GEIGEIGEIST/TOTEM/docs/images/TOTEM_black_tenting_bottom.jpg

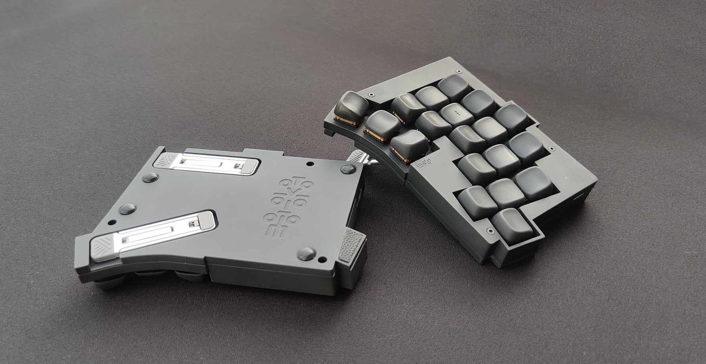
docs/images/TOTEM_black_tenting_bottom.jpg
