GEIGEIGEIST/TOTEM/docs/images/TOTEM_clayrender_01.jpg

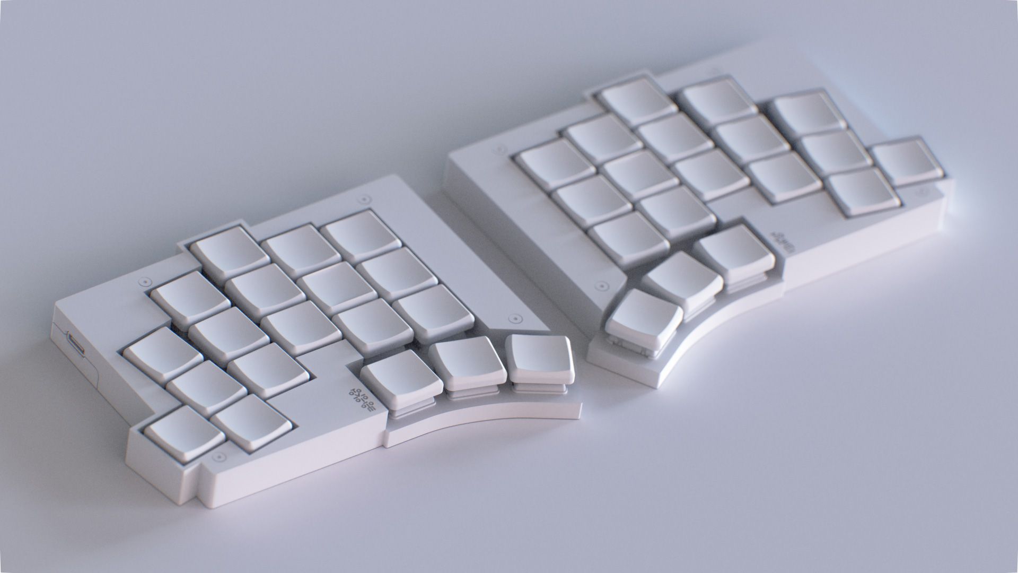
docs/images/TOTEM_clayrender_01.jpg
