GEIGEIGEIST/TOTEM/docs/images/TOTEM_clayrender_02.jpg

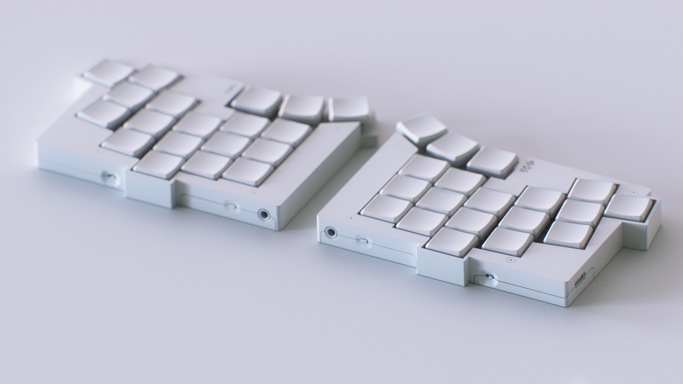
docs/images/TOTEM_clayrender_02.jpg
