GEIGEIGEIST/TOTEM/docs/images/TOTEM_layout.png

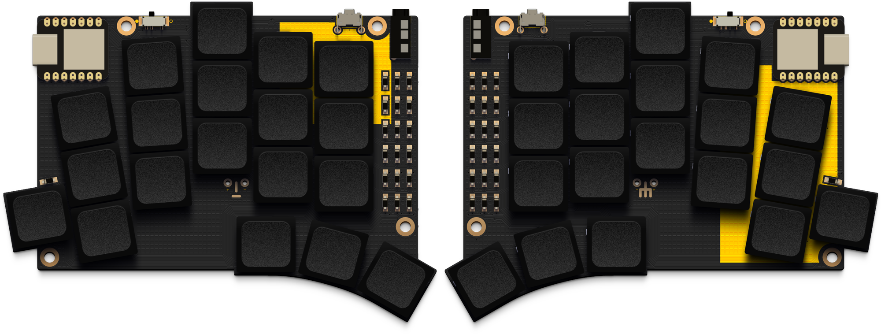
docs/images/TOTEM_layout.png
