GEIGEIGEIST/TOTEM/PCB/totem_0-3/TOTEM3D/PJ320A.STEP

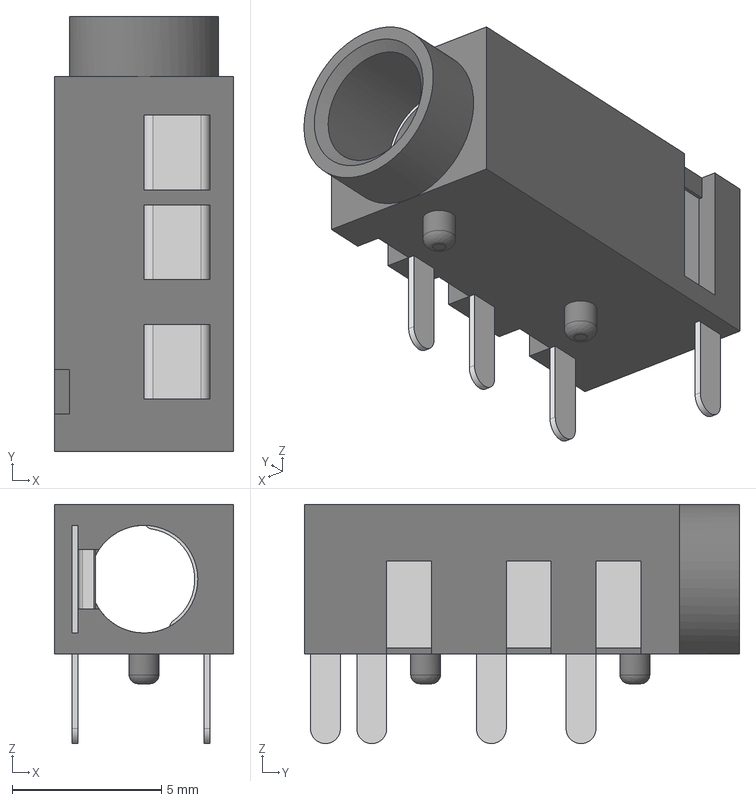
[picture p21: CAD file, 2022-11-10]
PCB/totem_0-3/TOTEM3D/PJ320A.STEP
6.00 x 14.6 x 8.00 mm
