GEIGEIGEIST/TOTEM/PCB/totem_0-3/TOTEM3D/D_SOD-123.step

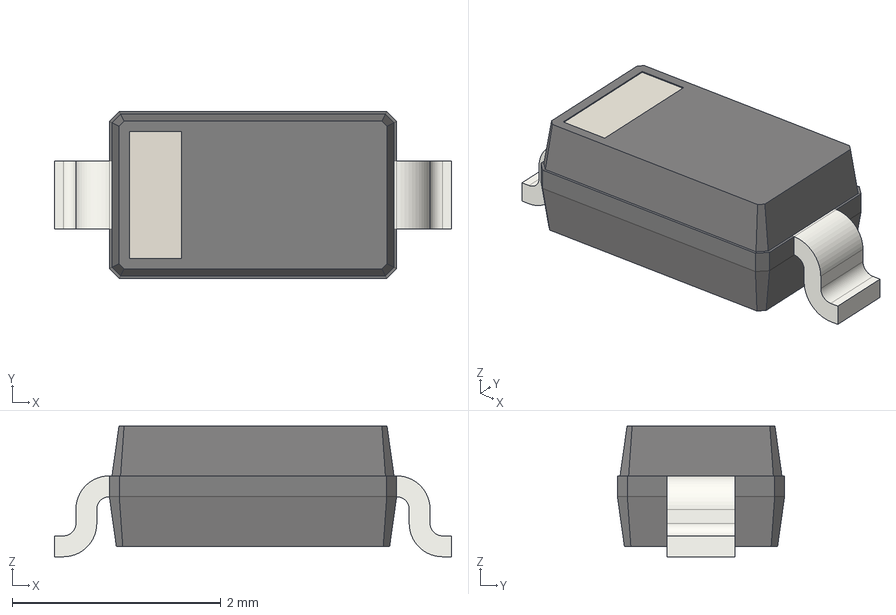
[picture p22: CAD file, 2022-11-10]
PCB/totem_0-3/TOTEM3D/D_SOD-123.step
3.80 x 1.60 x 1.25 mm
