GEIGEIGEIST/TOTEM/PCB/totem_0-3/TOTEM3D/xiao-ble-tht.step

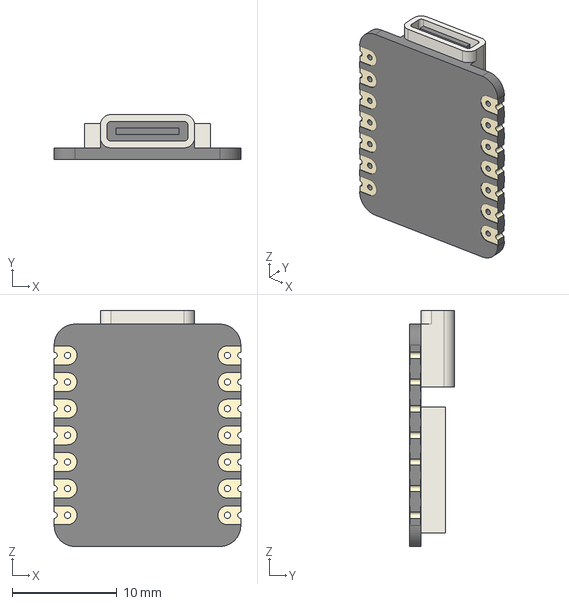
[picture p23: CAD file, 2022-11-10]
PCB/totem_0-3/TOTEM3D/xiao-ble-tht.step
17.8 x 4.27 x 22.5 mm
