GEIGEIGEIST/TOTEM/PCB/totem_0-3/TOTEM3D/MSK12C02.STEP

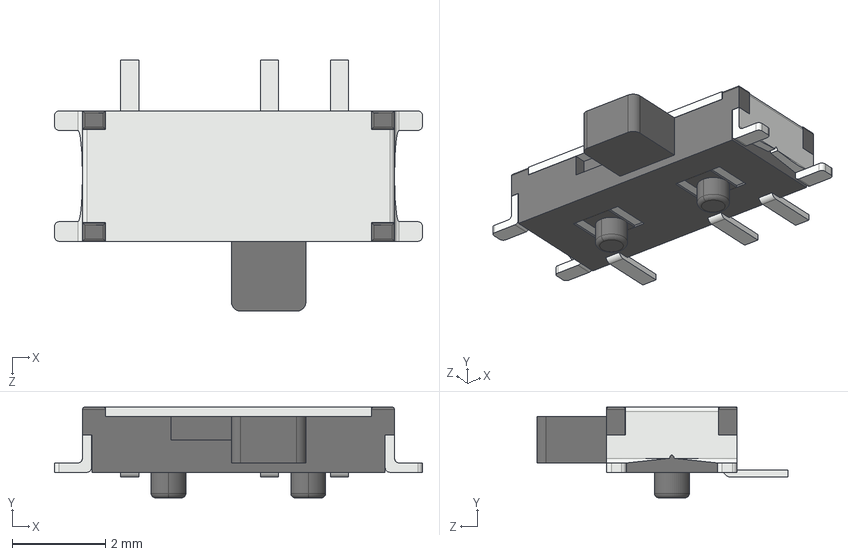
[picture p24: CAD file, 2022-11-10]
PCB/totem_0-3/TOTEM3D/MSK12C02.STEP
7.90 x 1.95 x 5.39 mm
