GEIGEIGEIST/TOTEM/PCB/totem_0-3/TOTEM3D/Kailh_socket_PG1350_optional.STEP

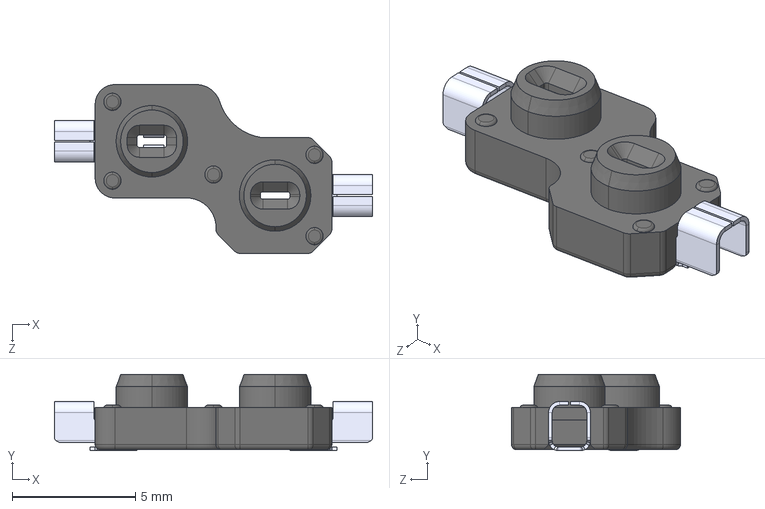
[picture p25: CAD file, 2022-11-10]
PCB/totem_0-3/TOTEM3D/Kailh_socket_PG1350_optional.STEP
12.9 x 3.09 x 6.85 mm
pin x 2
socket
