GEIGEIGEIST/TOTEM/PCB/totem_0-3/totem_0_3.kicad_sch

## KiCad design PCB/totem_0-3/totem_0_3.kicad_sch (2022-11-10)

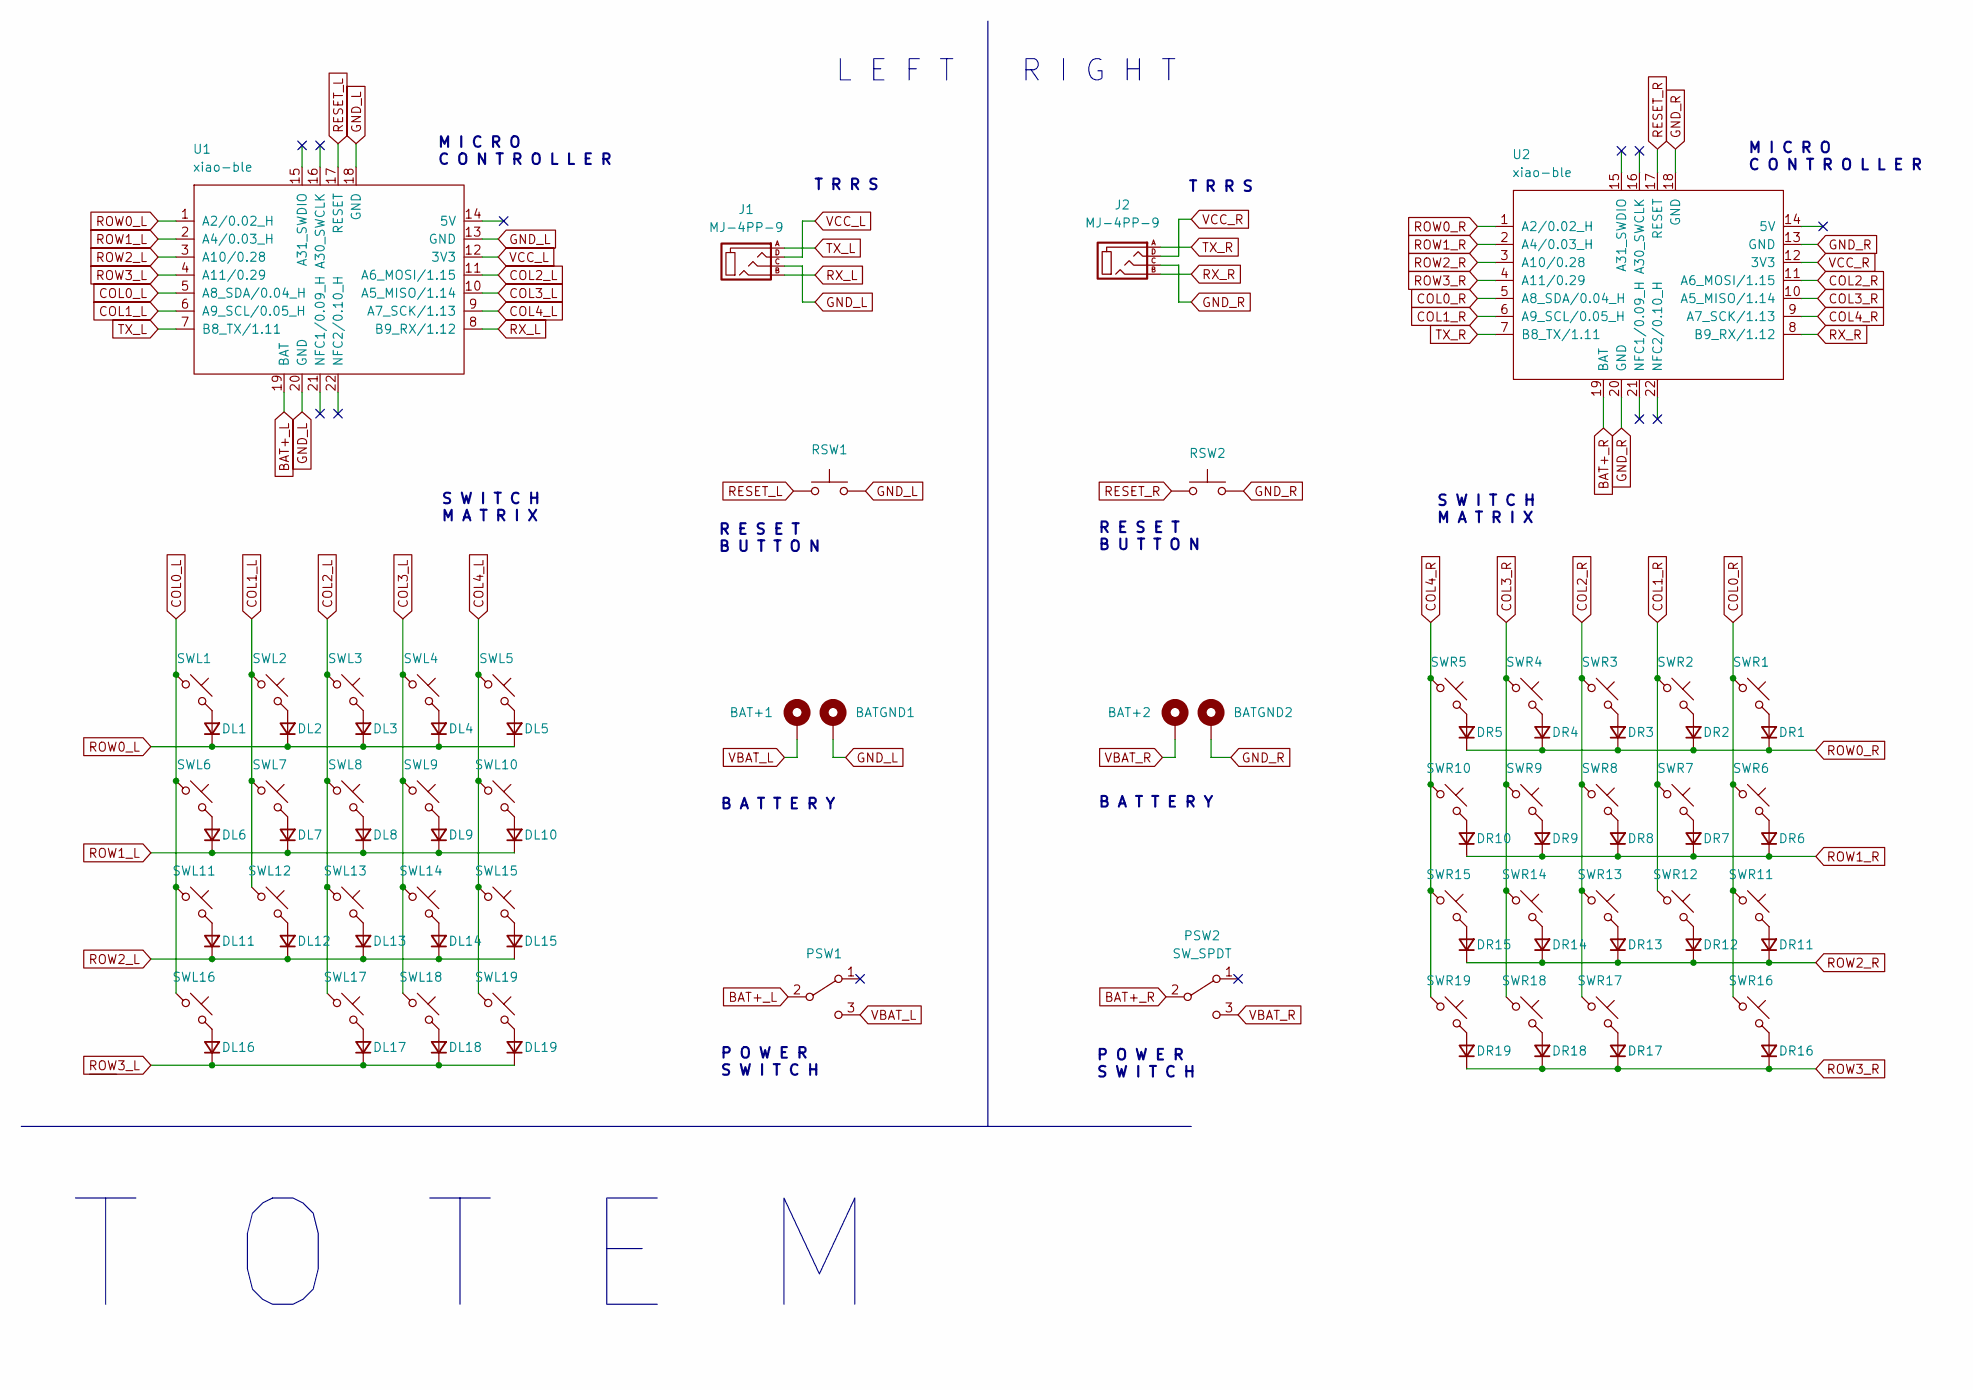
[picture p57: schematic totem_0_3.kicad_sch]

Parts:
BAT+1, BAT+2: +; BatteryPad
BATGND1, BATGND2: -; BatteryPad
DL1, DL2, DL3, DL4, DL5, DL6, DL7, DL8, DL9, DL10, DL11, DL12, DL13, DL14, DL15, DL16, DL17, DL18, DL19: D_Small; Diode_SOD123
DR1, DR2, DR3, DR4, DR5, DR6, DR7, DR8, DR9, DR10, DR11, DR12, DR13, DR14, DR15, DR16, DR17, DR18, DR19: D_Small; Diode_SOD123
J1, J2: MJ-4PP-9; MJ-4PP-9_1side
PSW1, PSW2: SW_SPDT; MSK12C02
RSW1, RSW2: SW_Push; SKHLLCA010
SWL1, SWL2, SWL3, SWL4, SWL5, SWL6, SWL7, SWL8, SWL9, SWL10, SWL11, SWL12, SWL13, SWL14, SWL15, SWL16, SWL17, SWL18, SWL19: SW_Push_45deg; Kailh_socket_PG1350_optional
SWR1, SWR2, SWR3, SWR4, SWR5, SWR6, SWR7, SWR8, SWR9, SWR10, SWR11, SWR12, SWR13, SWR14, SWR15, SWR16, SWR17, SWR18, SWR19: SW_Push_45deg; Kailh_socket_PG1350_optional
U1, U2: xiao-ble; xiao-ble-smd-cutout

Connections:
BAT+_L: PSW1.2 (B), U1.19 (BAT)
BAT+_R: PSW2.2 (B), U2.19 (BAT)
COL0_L: SWL1.1, SWL6.1, SWL11.1, SWL16.1, U1.5 (A8_SDA/0.04_H)
COL0_R: SWR1.1, SWR6.1, SWR11.1, SWR16.1, U2.5 (A8_SDA/0.04_H)
COL1_L: SWL2.1, SWL7.1, SWL12.1, U1.6 (A9_SCL/0.05_H)
COL1_R: SWR2.1, SWR7.1, SWR12.1, U2.6 (A9_SCL/0.05_H)
COL2_L: SWL3.1, SWL8.1, SWL13.1, SWL17.1, U1.11 (A6_MOSI/1.15)
COL2_R: SWR3.1, SWR8.1, SWR13.1, SWR17.1, U2.11 (A6_MOSI/1.15)
COL3_L: SWL4.1, SWL9.1, SWL14.1, SWL18.1, U1.10 (A5_MISO/1.14)
COL3_R: SWR4.1, SWR9.1, SWR14.1, SWR18.1, U2.10 (A5_MISO/1.14)
COL4_L: SWL5.1, SWL10.1, SWL15.1, SWL19.1, U1.9 (A7_SCK/1.13)
COL4_R: SWR5.1, SWR10.1, SWR15.1, SWR19.1, U2.9 (A7_SCK/1.13)
GND_L: BATGND1.1, J1.C, RSW1.2, U1.13 (GND), U1.18 (GND), U1.20 (GND)
GND_R: BATGND2.1, J2.C, RSW2.2, U2.13 (GND), U2.18 (GND), U2.20 (GND)
unnamed: DL1.2 (A), SWL1.2
unnamed: DL2.2 (A), SWL2.2
unnamed: DL3.2 (A), SWL3.2
unnamed: DL4.2 (A), SWL4.2
unnamed: DL5.2 (A), SWL5.2
unnamed: DL6.2 (A), SWL6.2
unnamed: DL7.2 (A), SWL7.2
unnamed: DL8.2 (A), SWL8.2
unnamed: DL9.2 (A), SWL9.2
unnamed: DL10.2 (A), SWL10.2
unnamed: DL11.2 (A), SWL11.2
unnamed: DL12.2 (A), SWL12.2
unnamed: DL13.2 (A), SWL13.2
unnamed: DL14.2 (A), SWL14.2
unnamed: DL15.2 (A), SWL15.2
unnamed: DL16.2 (A), SWL16.2
unnamed: DL17.2 (A), SWL17.2
unnamed: DL18.2 (A), SWL18.2
unnamed: DL19.2 (A), SWL19.2
unnamed: DR1.2 (A), SWR1.2
unnamed: DR2.2 (A), SWR2.2
unnamed: DR3.2 (A), SWR3.2
unnamed: DR4.2 (A), SWR4.2
unnamed: DR5.2 (A), SWR5.2
unnamed: DR6.2 (A), SWR6.2
unnamed: DR7.2 (A), SWR7.2
unnamed: DR8.2 (A), SWR8.2
unnamed: DR9.2 (A), SWR9.2
unnamed: DR10.2 (A), SWR10.2
unnamed: DR11.2 (A), SWR11.2
unnamed: DR12.2 (A), SWR12.2
unnamed: DR13.2 (A), SWR13.2
unnamed: DR14.2 (A), SWR14.2
unnamed: DR15.2 (A), SWR15.2
unnamed: DR16.2 (A), SWR16.2
unnamed: DR17.2 (A), SWR17.2
unnamed: DR18.2 (A), SWR18.2
unnamed: DR19.2 (A), SWR19.2
RESET_L: RSW1.1, U1.17 (RESET)
RESET_R: RSW2.1, U2.17 (RESET)
ROW0_L: DL1.1 (K), DL2.1 (K), DL3.1 (K), DL4.1 (K), DL5.1 (K), U1.1 (A2/0.02_H)
ROW0_R: DR1.1 (K), DR2.1 (K), DR3.1 (K), DR4.1 (K), DR5.1 (K), U2.1 (A2/0.02_H)
ROW1_L: DL6.1 (K), DL7.1 (K), DL8.1 (K), DL9.1 (K), DL10.1 (K), U1.2 (A4/0.03_H)
ROW1_R: DR6.1 (K), DR7.1 (K), DR8.1 (K), DR9.1 (K), DR10.1 (K), U2.2 (A4/0.03_H)
ROW2_L: DL11.1 (K), DL12.1 (K), DL13.1 (K), DL14.1 (K), DL15.1 (K), U1.3 (A10/0.28)
ROW2_R: DR11.1 (K), DR12.1 (K), DR13.1 (K), DR14.1 (K), DR15.1 (K), U2.3 (A10/0.28)
ROW3_L: DL16.1 (K), DL17.1 (K), DL18.1 (K), DL19.1 (K), U1.4 (A11/0.29)
ROW3_R: DR16.1 (K), DR17.1 (K), DR18.1 (K), DR19.1 (K), U2.4 (A11/0.29)
RX_L: J1.B, U1.8 (B9_RX/1.12)
RX_R: J2.B, U2.8 (B9_RX/1.12)
TX_L: J1.A, U1.7 (B8_TX/1.11)
TX_R: J2.A, U2.7 (B8_TX/1.11)
VBAT_L: BAT+1.1, PSW1.3 (C)
VBAT_R: BAT+2.1, PSW2.3 (C)
VCC_L: J1.D, U1.12 (3V3)
VCC_R: J2.D, U2.12 (3V3)

Notes on the sheet:
M I C R O C O N T R O L L E R
T R R S
R E S E T B U T T O N
S W I T C H M A T R I X
P O W E R S W I T C H
T O T E M
B A T T E R Y
R I G H T
L E F T
